lfantoniosi/tn_vdp/fpga/tn_vdp_v3_v9958/src/SPI_MCP3202.v

`timescale 1ns / 1ns

/////////////////////////////////////////////////////////////////////////////////////////
//
//   PROJECT DESCRIPTION:	A SPI master for a MCP3202 12-bit ADC. The sampling frequency
// 							is 50 KHz, making the Nyquist frequency 25 KHz. When the
//                          output 12-bit word is valid, the data valid flag goes high.
//                          The module can be configured to support single-ended and 
//							differential sampling modes, as well as specificy aquisition 
//                          channel on the ADC (see pinout in datasheet for details). 
//                          The ADC runs in MSB-first mode ONLY to maximize speed.
//
//	            FILENAME:   SPI_MCP3202.v
//	             VERSION:   2.0  9/17/2020
//                AUTHOR:   Dominic Meads
//
/////////////////////////////////////////////////////////////////////////////////////////


module SPI_MCP3202 #( // set up bits for MOSI (DIN on datasheet) 
	parameter SGL = 1,        // sets ADC to single ended mode
	parameter ODD = 0         // sets sample input to channel 0
	)(
	input clk,                 // 125  MHz 
	input EN,                  // Enable the SPI core (ACTIVE HIGH)
	input MISO,                // data out of ADC (Dout pin)
	output MOSI,               // Data into ADC (Din pin)
    output SCK_ENABLE,
	output [11:0] o_DATA,      // 12 bit word (for other modules)
	output CS,                 // Chip Select
	output DATA_VALID          // is high when there is a full 12 bit word. 
	);
	
	// additional MOSI data
	localparam START = 1;           // start bit
	localparam	MSBF = 1;           // sets ADC to transmit MSB first
	
	// states
	localparam DISABLE = 1;         // CS is high
	localparam TRANSMITTING = 2;    // set the sample channel, sampling mode, etc...
	localparam RECEIVING = 3;       // convert the bitstream into parellel word
	
	integer i = 0;                  // for the for loop in the TRANSMITTING state (used to condense code)
	
	reg [7:0] SCK_counter = 0;       // for the output SPI clock
	reg r_MOSI = 0; 
	reg [11:0] r_DATA;
	reg [1:0] r_STATE = DISABLE;     // state machine (init to disable state)
	reg r_CS = 1;       	         // disable CS to start
	reg r_SCK_enable = 0;            // enable for SCK
	reg r_DV = 0;                    // DATA_VALID register
	reg [11:0] sample_counter = 1;   // this counter flips over after one sample period
	                                      // it starts at one so INITIALIZE waits one sampling period to begin DISABLE
	 
	// sample_counter
	always @ (posedge clk)                       
		begin 
		    if (EN)
		        begin      
                    if (sample_counter <= 2698)           /* this number is the amount of system clock cycles to finish one sampling period: 
                                                             2500 counts (0-2499) @ 8ns system clock period = 20us or 50 KHz */
                                                             
                        sample_counter <= sample_counter + 1;  // sample counter only counts if enable is high
                    else 
                        sample_counter <= 0;
                end  // if (EN)
            else  // if EN low, reset sample counter
                sample_counter <= 0; 
		end   // end sample_counter
		
	// SPI_CLK
    reg SCK_clk;
                                                  	
    assign SCK_ENABLE = r_SCK_enable;

	// State machine	
	always @ (posedge clk)
		begin 
			case (r_STATE)
			
				DISABLE:              
					begin 
						r_CS <= 1;
						r_SCK_enable <= 0;
						r_MOSI <= 0;
						r_DV <= 0;
						
							if (sample_counter == 68 && EN)     // ensures that DISABLE waits 64 counts or 512ns (tcsh must >= 500ns in datasheet)
								begin 
									r_STATE <= TRANSMITTING;
									r_CS <= 0;                       // CS pulled low, activates sampling
						            r_MOSI <= START;
								end  // if (sample_counter == ...
								
							else 
								r_STATE <= DISABLE;
					end     // end DISABLE 
					
					
				TRANSMITTING:
					begin 
						r_CS <= 0;                       // CS pulled low, activates sampling
						r_SCK_enable <= 0;
						r_MOSI <= START;
						r_DV <= 0;
						
							if (sample_counter >= 129 && EN)     
								r_SCK_enable <= 1;   // pull SCK high after 56 counts @ 8ns (448ns, check tsucs in datasheet, tsucs >= 100ns)

							if (sample_counter >= 205 && sample_counter < 356 && EN)
									r_MOSI <= SGL;        // provides set up data to ADC depending on the timing
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
